whatamIdoingYT/prusa-mini-corexy-parts/assets/SpacerShims/Spacer106.stl

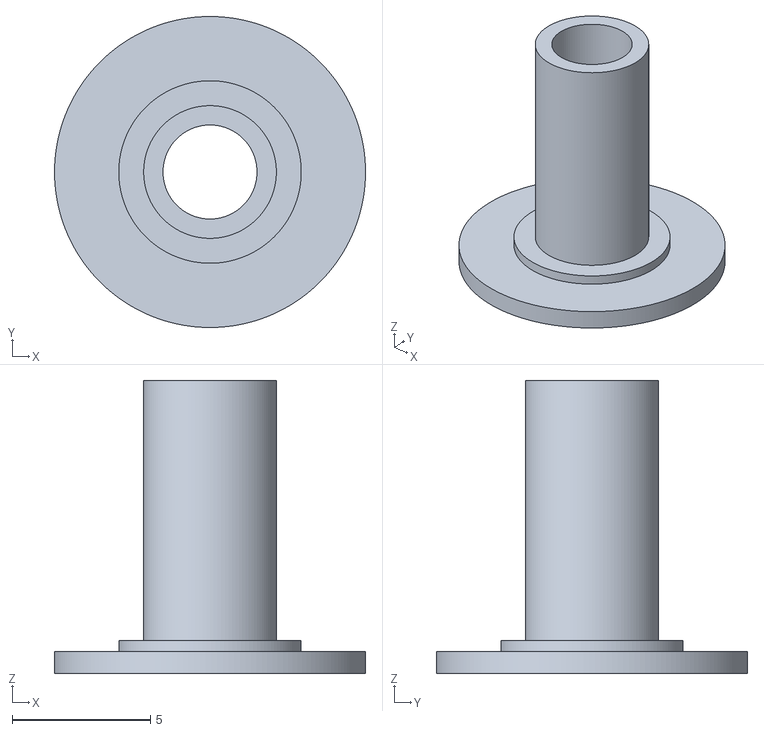
[picture p15: CAD file, 2026-03-22]
assets/SpacerShims/Spacer106.stl
11.2 x 11.2 x 10.6
